alinxalinx/Z19_P/linux/.images_for_documents/1.png

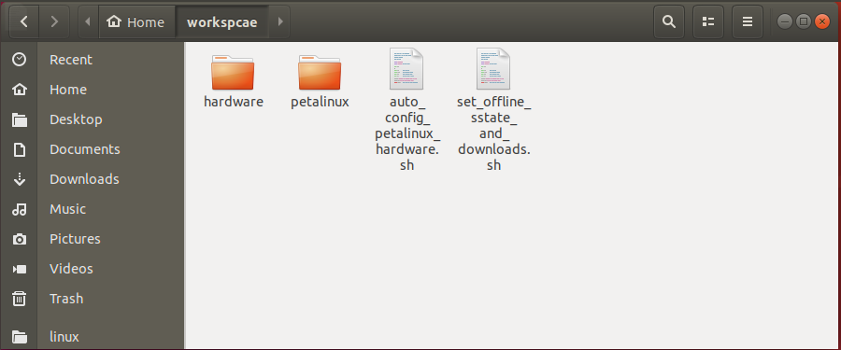
linux/.images_for_documents/1.png
