alinxalinx/Z19_P/linux/.images_for_documents/2.png

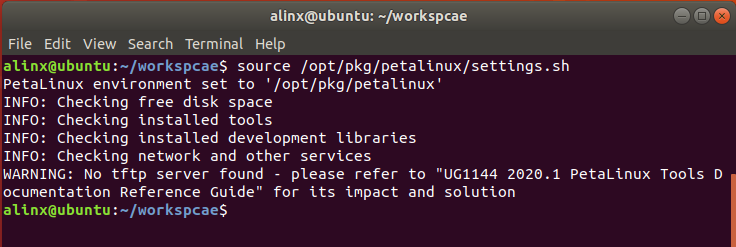
linux/.images_for_documents/2.png
