alinxalinx/Z19_P/linux/.images_for_documents/3.png

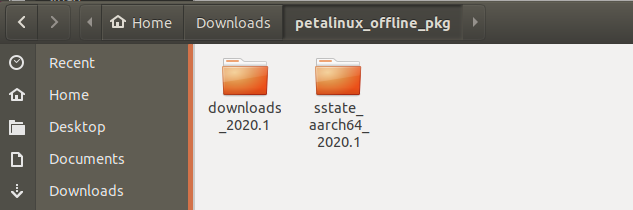
linux/.images_for_documents/3.png
