alinxalinx/Z19_P/linux/.images_for_documents/5.png

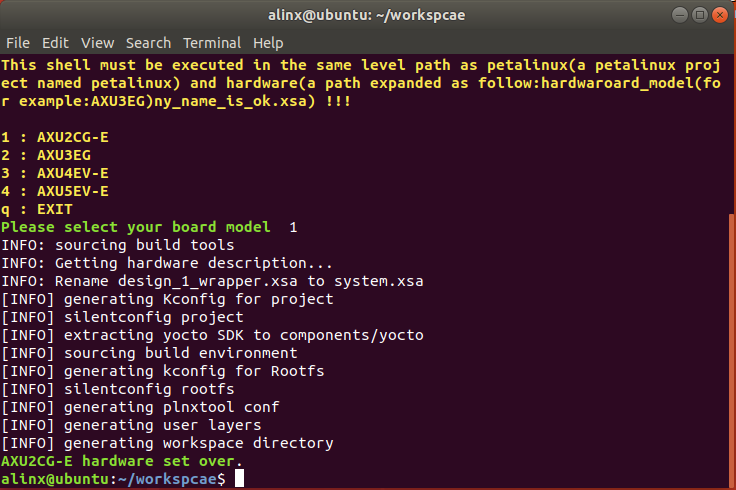
linux/.images_for_documents/5.png
