alinxalinx/Z19_P/linux/.images_for_documents/6.png

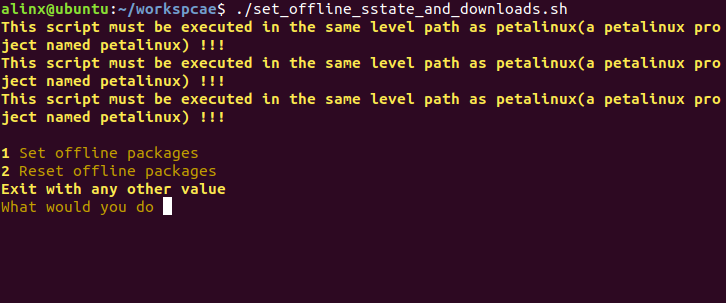
linux/.images_for_documents/6.png
