alinxalinx/Z19_P/linux/.images_for_documents/7.png

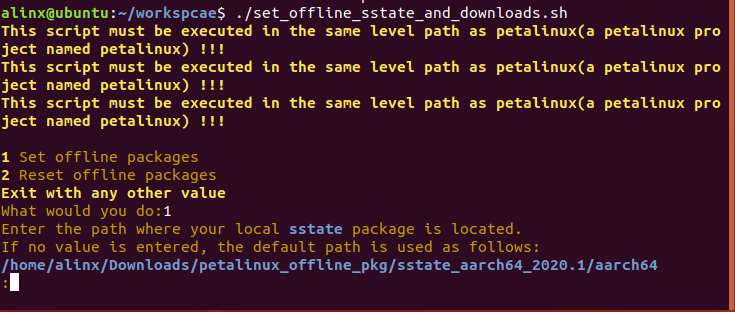
linux/.images_for_documents/7.png
