alinxalinx/Z19_P/linux/.images_for_documents/12.png

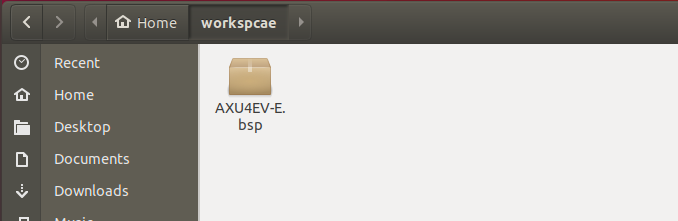
linux/.images_for_documents/12.png
