alinxalinx/Z19_P/linux/.images_for_documents/14.png

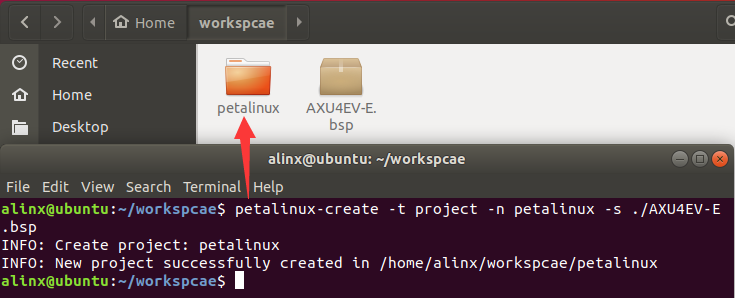
linux/.images_for_documents/14.png
