alinxalinx/Z19_P/linux/.images_for_documents/40.png

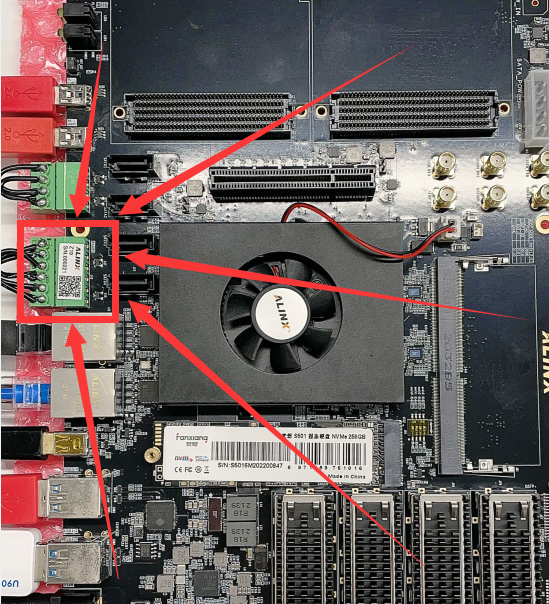
linux/.images_for_documents/40.png
