alinxalinx/Z19_P/linux/.images_for_documents/41.png

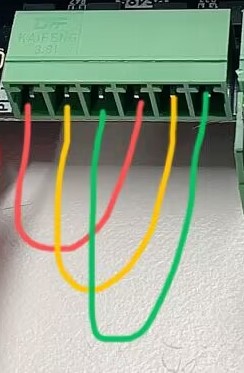
linux/.images_for_documents/41.png
