alinxalinx/Z19_P/linux/.images_for_documents/43.png

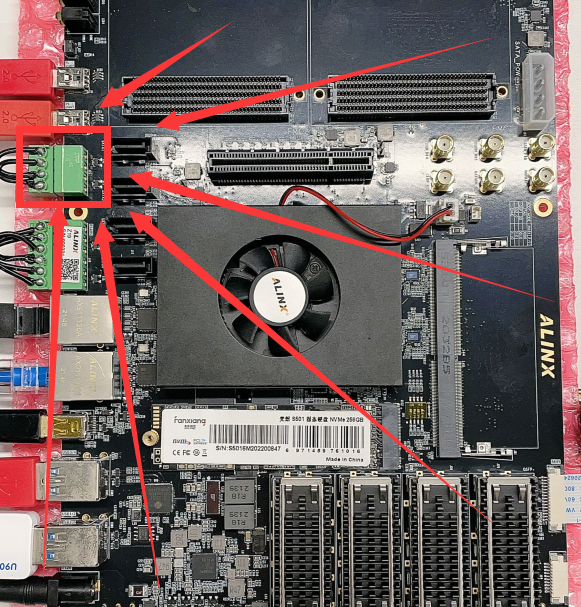
linux/.images_for_documents/43.png
