alinxalinx/Z19_P/linux/.images_for_documents/44.png

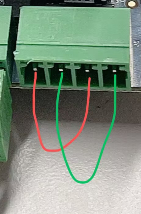
linux/.images_for_documents/44.png
