alinxalinx/Z19_P/linux/.images_for_documents/46.png

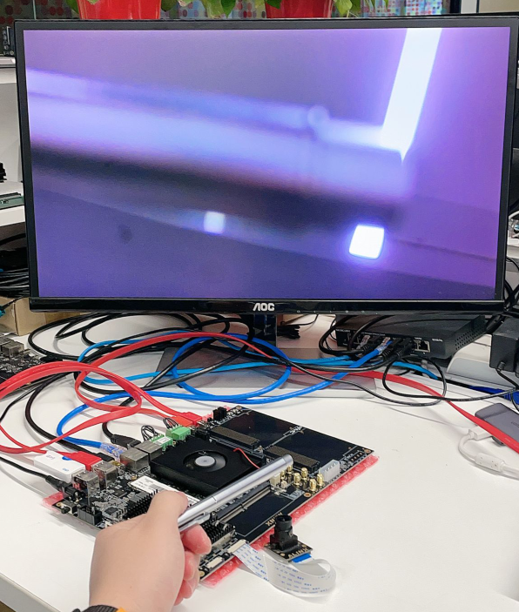
linux/.images_for_documents/46.png
