alinxalinx/Z19_P/linux/.images_for_documents/48.png

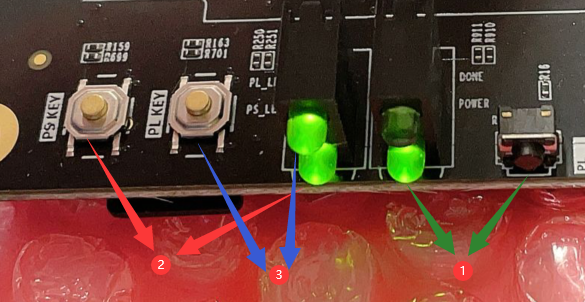
linux/.images_for_documents/48.png
