alinxalinx/Z19_P/linux/.images_for_documents/66.png

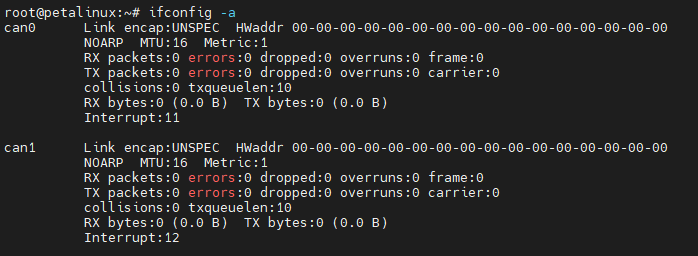
linux/.images_for_documents/66.png
