alinxalinx/Z19_P/linux/.images_for_documents/67.png

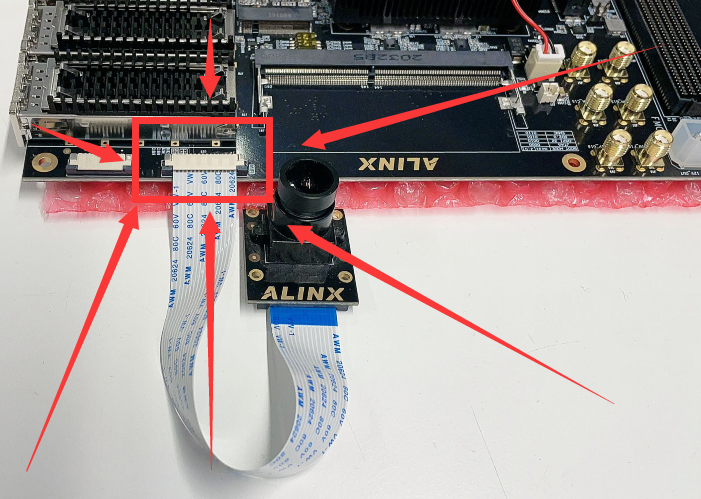
linux/.images_for_documents/67.png
