alinxalinx/Z19_P/linux/.images_for_documents/68.png

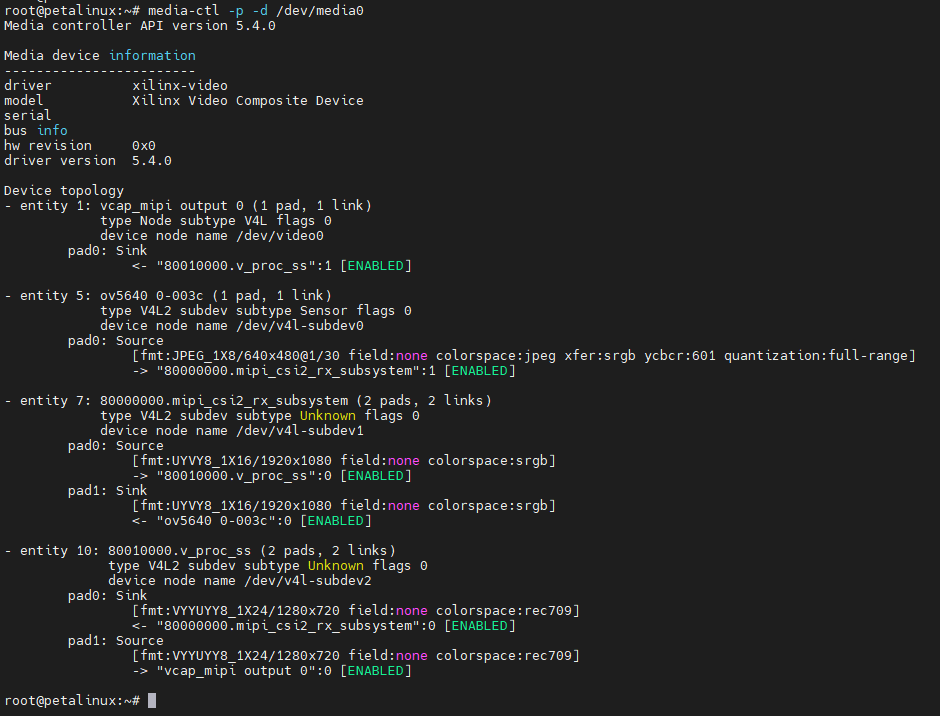
linux/.images_for_documents/68.png
