alinxalinx/Z19_P/linux/.images_for_documents/70.png

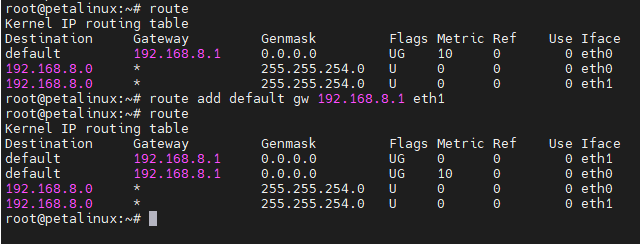
linux/.images_for_documents/70.png
