alinxalinx/Z19_P/linux/.images_for_documents/71.png

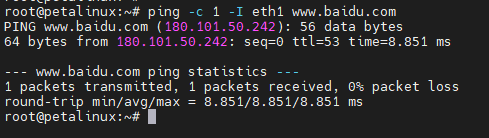
linux/.images_for_documents/71.png
